IDMNYU/synthaccess/MIDItoRBD/RBD.png

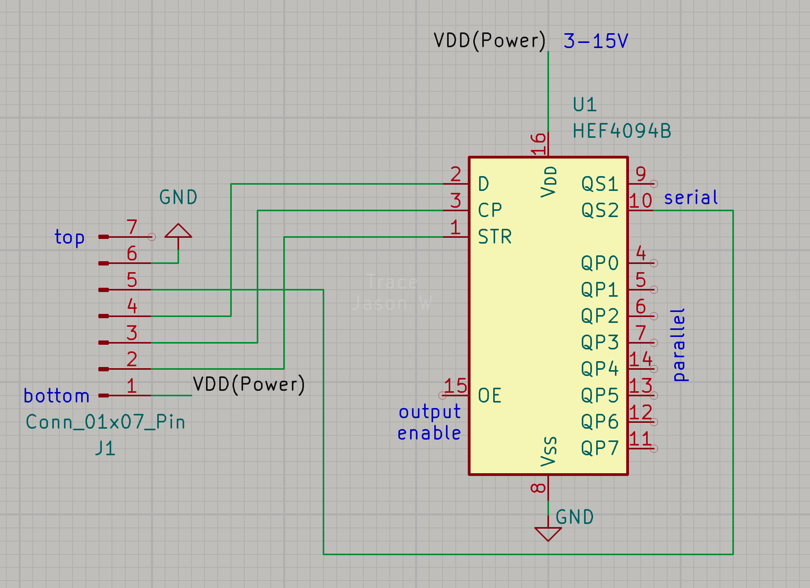
MIDItoRBD/RBD.png
