IDMNYU/synthaccess/hapticDriver/foo/spicetest/spicetest.kicad_pcb

## KiCad design Schematics/shematics angle cal/shematics angle cal.kicad_sch

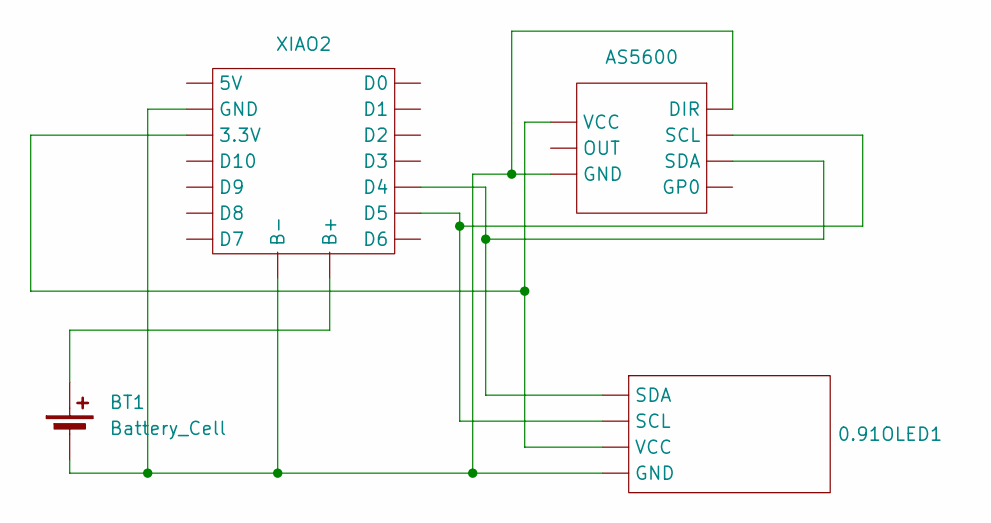
[picture p103: schematic shematics angle cal.kicad_sch]

Parts:
0.91OLED1: (no value)
AS5600: (no value)
BT1: Battery_Cell
XIAO2: (no value)

Connections:
unnamed: 0.91OLED1., AS5600., BT1.2 (-), XIAO2.
unnamed: BT1.1 (+), XIAO2.
